lucasantoro/Sunrise/communications/openvlc/firmware-v3/Core/Inc/usart.h

#ifndef __USART_H__
#define __USART_H__

#ifdef __cplusplus
extern "C" {
#endif

#include "main.h"

extern UART_HandleTypeDef huart3;
extern DMA_HandleTypeDef hdma_usart3_rx;
extern DMA_HandleTypeDef hdma_usart3_tx;

void MX_USART3_UART_Init(void);

#ifdef __cplusplus
}
#endif
#endif
